o5i/Automated-Microbrewery/Pics/20161009_160745.jpg

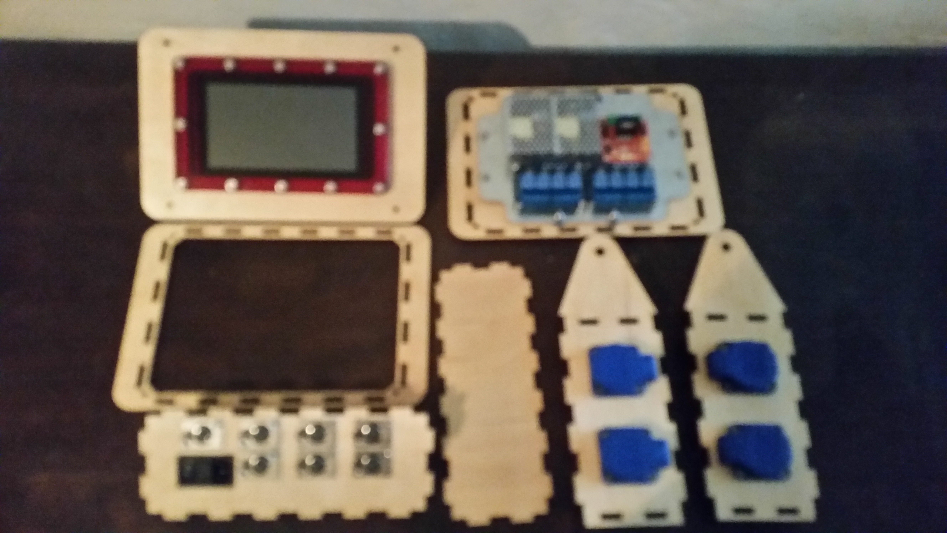
Pics/20161009_160745.jpg
