o5i/Automated-Microbrewery/E_control/Board_laylout/circuit.png

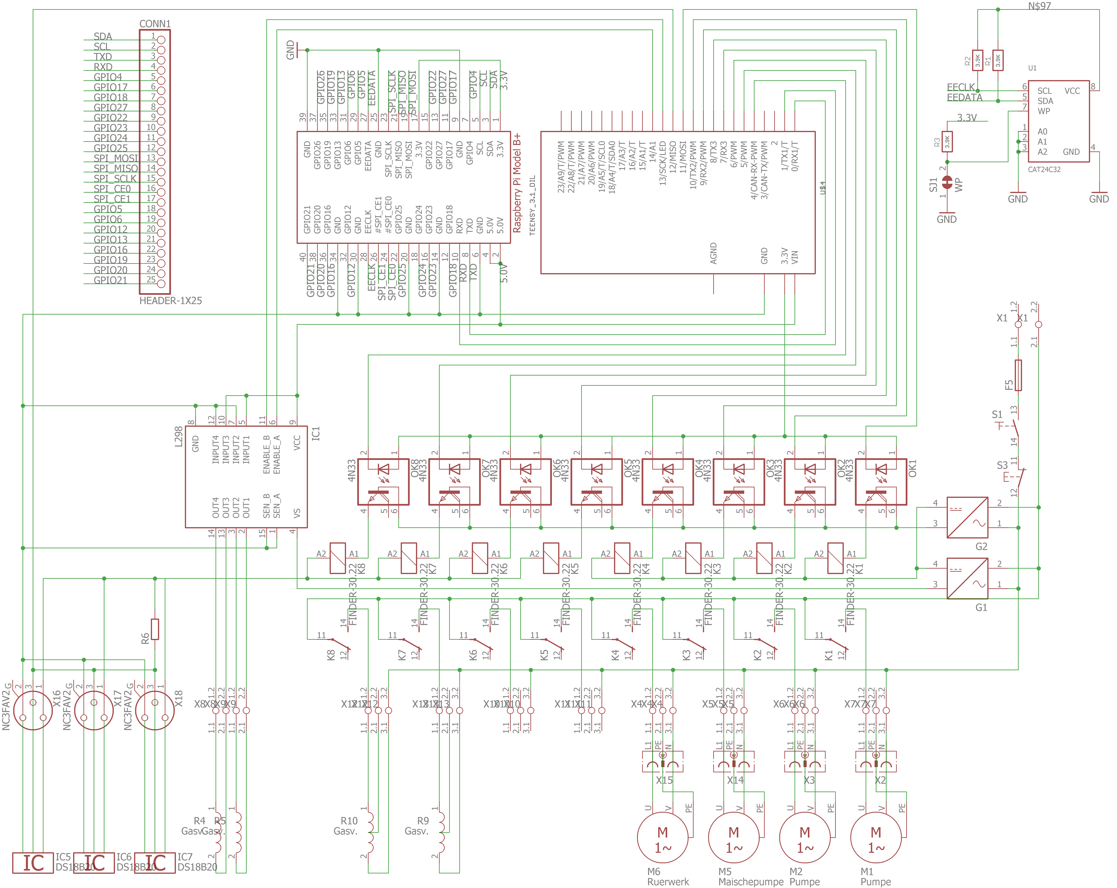
E_control/Board_laylout/circuit.png
