o5i/Automated-Microbrewery/E_control/Board_laylout/Eagle/Teensy3.2_v2.png

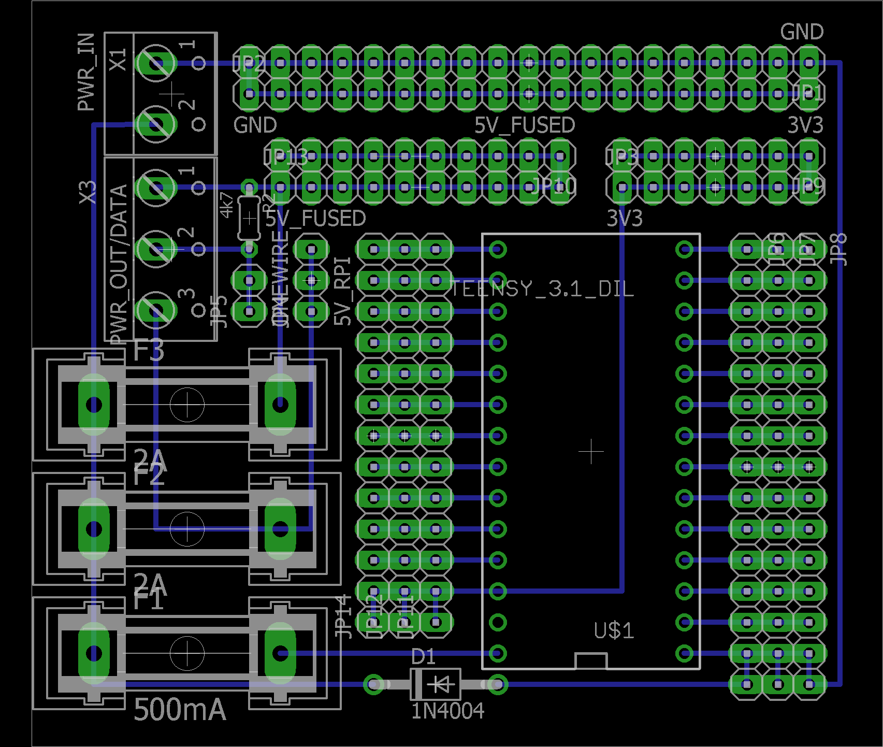
E_control/Board_laylout/Eagle/Teensy3.2_v2.png
