o5i/Automated-Microbrewery/E_control/Board_laylout/PT100.png

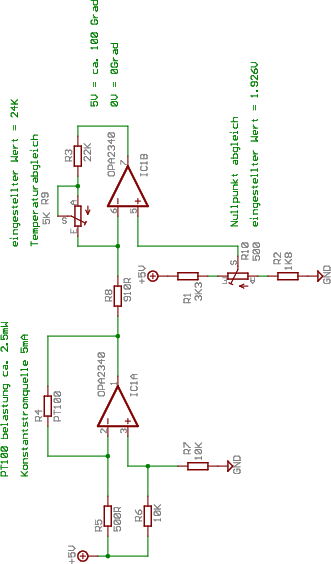
E_control/Board_laylout/PT100.png
