o5i/Automated-Microbrewery/E_control/Board_laylout/Teensy3.2_v2_circuit_brd.png

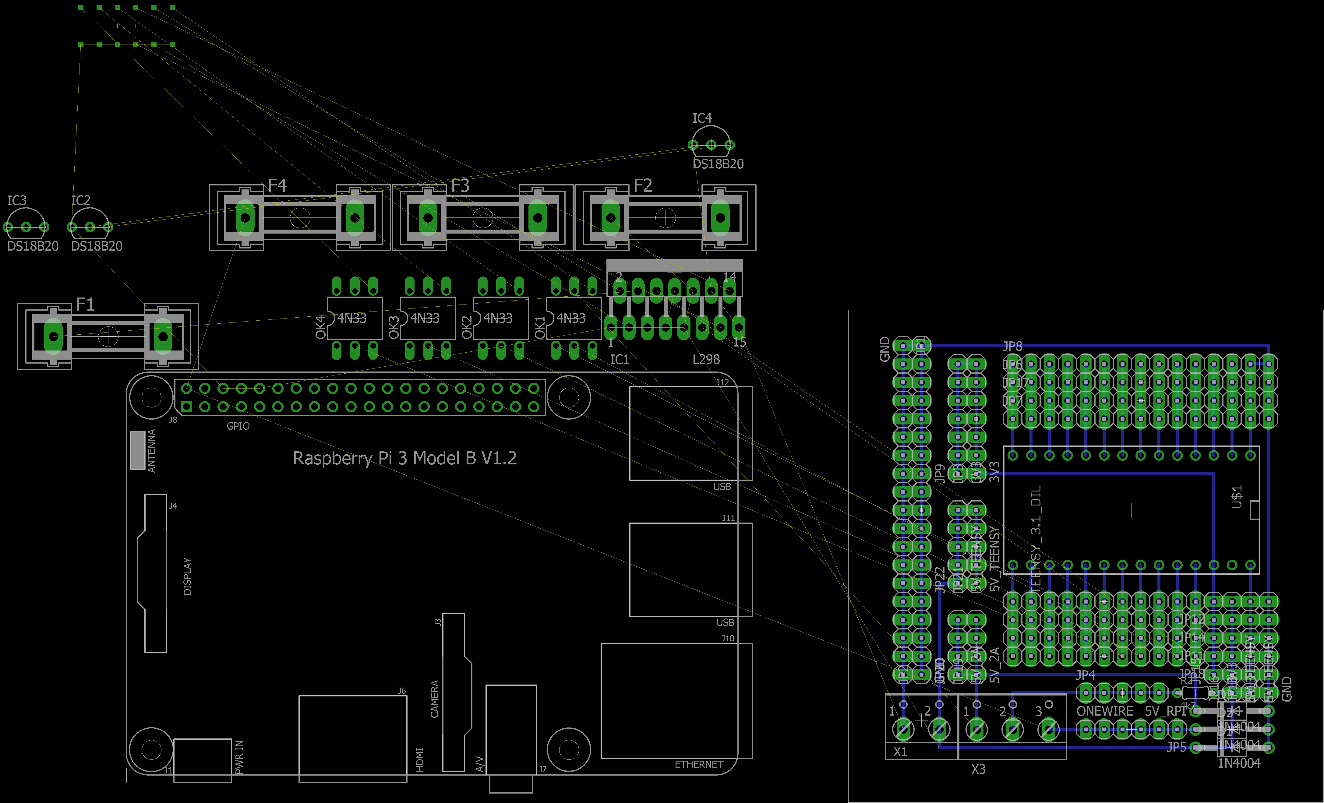
E_control/Board_laylout/Teensy3.2_v2_circuit_brd.png
