o5i/Automated-Microbrewery/E_control/PDF/HBridge.JPG

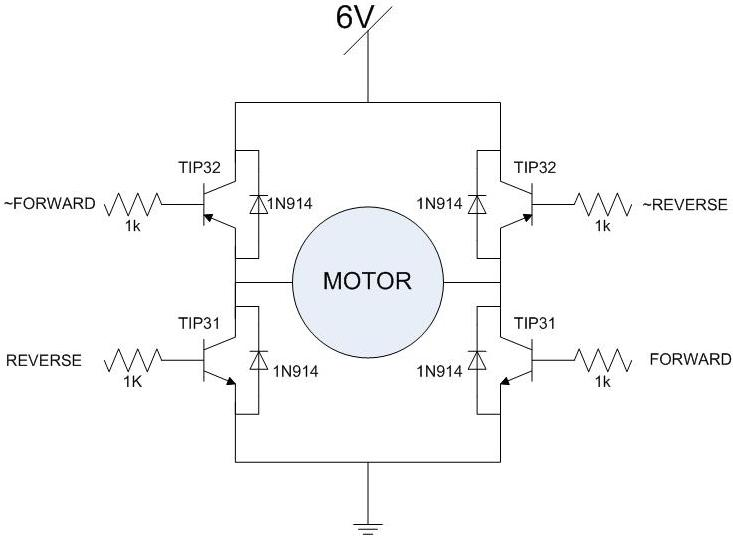
E_control/PDF/HBridge.JPG
