o5i/Automated-Microbrewery/E_control/PDF/plattev2.png

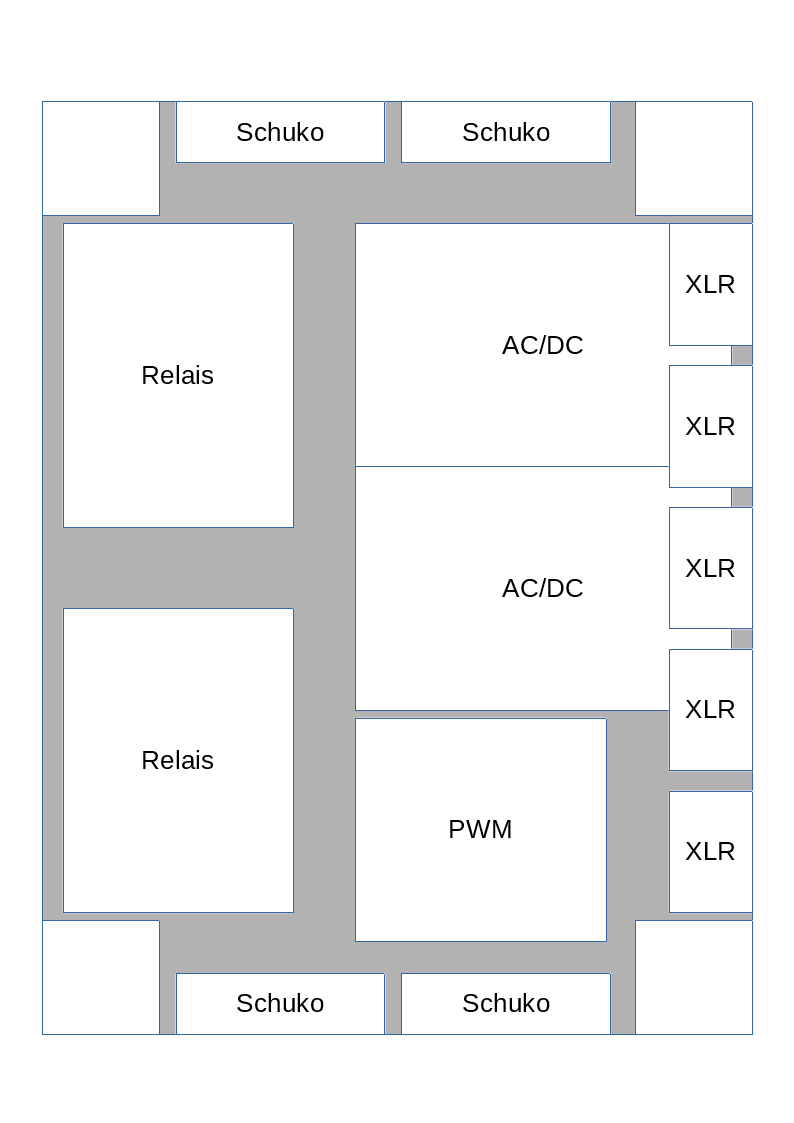
E_control/PDF/plattev2.png
