o5i/Automated-Microbrewery/Info/Frame/braumeister-200-liter-1.PNG

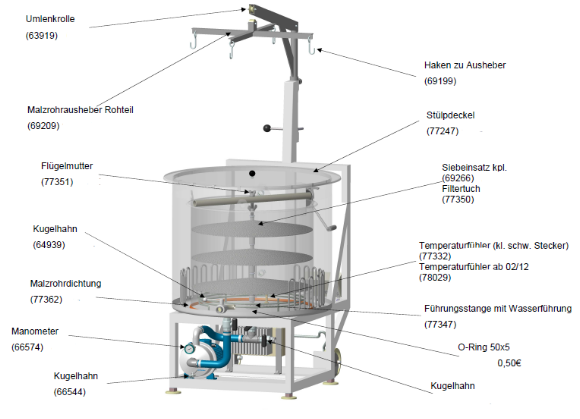
Info/Frame/braumeister-200-liter-1.PNG
