o5i/Automated-Microbrewery/Info/Frame/braumeister-200-liter-2.PNG

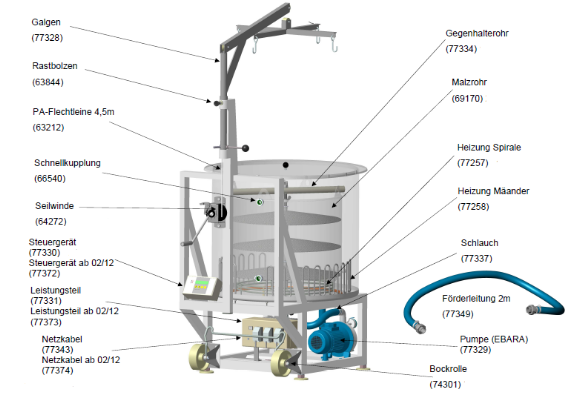
Info/Frame/braumeister-200-liter-2.PNG
