o5i/Automated-Microbrewery/Info/Frame/bruciatore_per_bollino_blu_caldaia.jpg

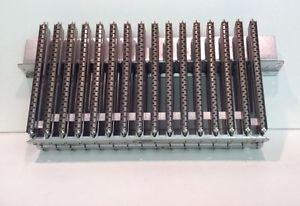
Info/Frame/bruciatore_per_bollino_blu_caldaia.jpg
