o5i/Automated-Microbrewery/Info/Frame/eintauchkuehler_1.jpg

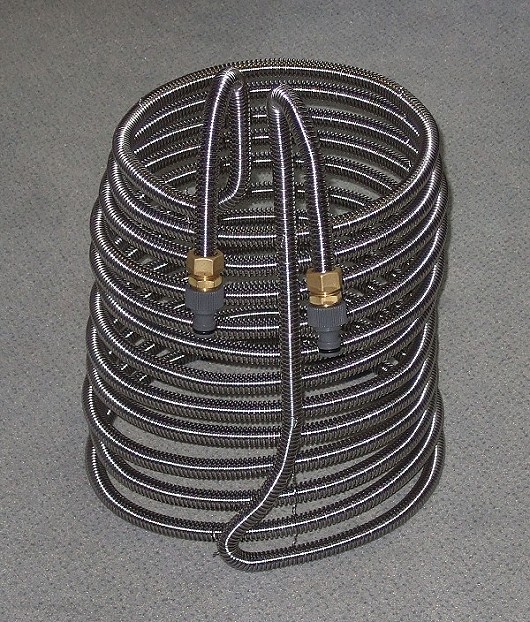
Info/Frame/eintauchkuehler_1.jpg
