o5i/Automated-Microbrewery/Info/Frame/HERMSv3.png

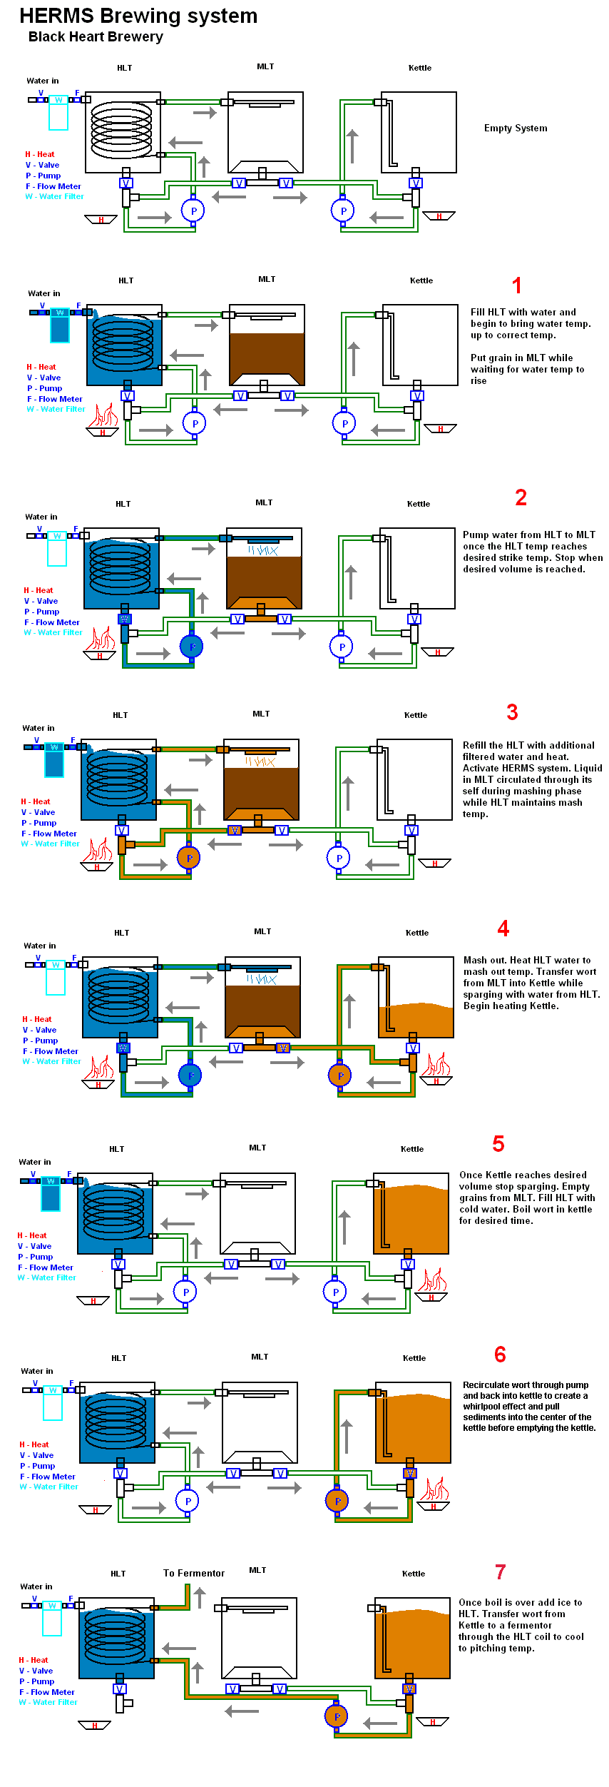
Info/Frame/HERMSv3.png
