o5i/Automated-Microbrewery/Info/Frame/HERMSv4.png

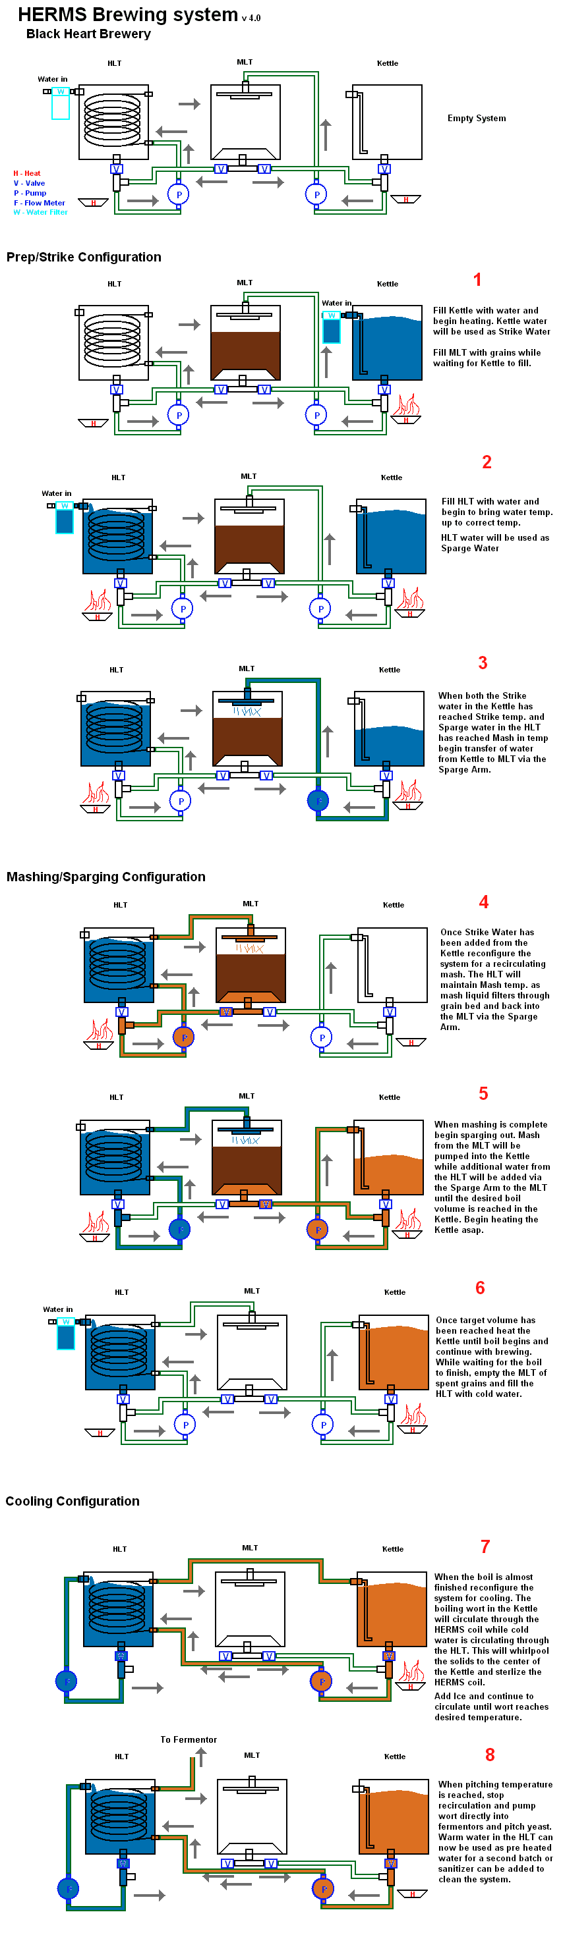
Info/Frame/HERMSv4.png
