o5i/Automated-Microbrewery/Info/Frame/RIMS.jpg

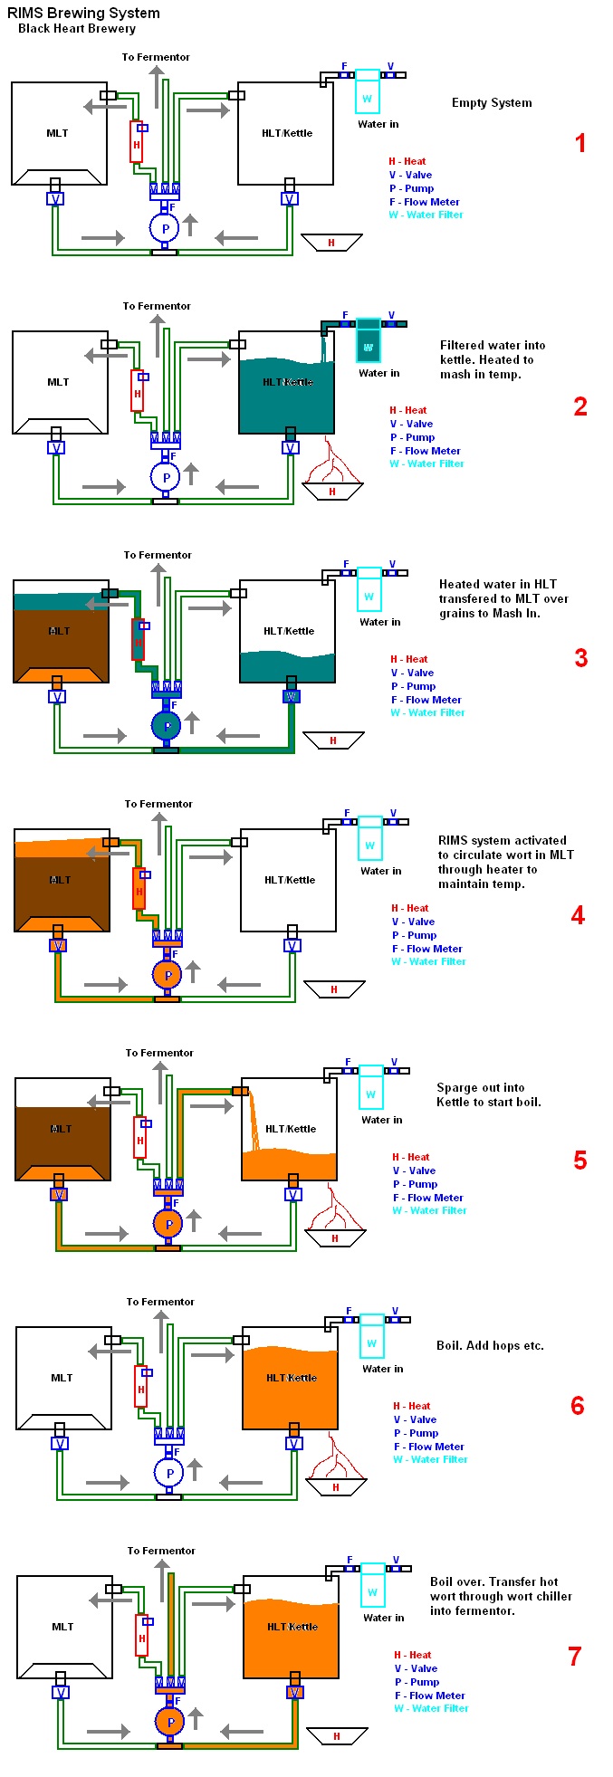
Info/Frame/RIMS.jpg
