o5i/Automated-Microbrewery/Info/Frame/s-l225.jpg

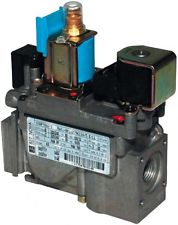
Info/Frame/s-l225.jpg
