o5i/Automated-Microbrewery/Info/Frame/Skizze.jpg

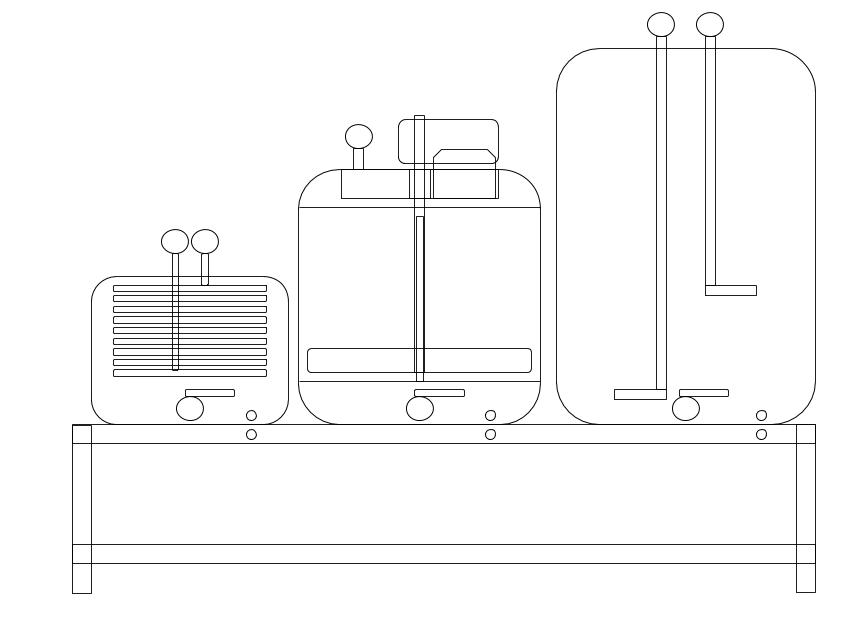
Info/Frame/Skizze.jpg
