o5i/Automated-Microbrewery/Info/Frame/Tisch_gestell.jpg

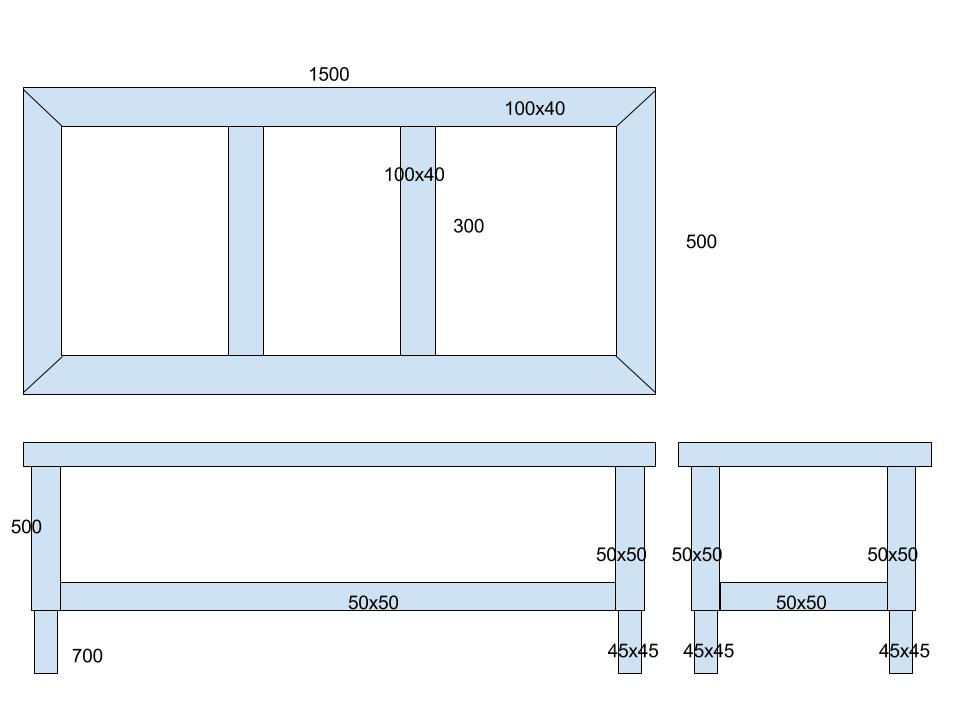
Info/Frame/Tisch_gestell.jpg
